krikun98/Skean/pcb/6col/skean.kicad_sch

## KiCad design pcb/6col/skean.kicad_sch (2023-03-14)

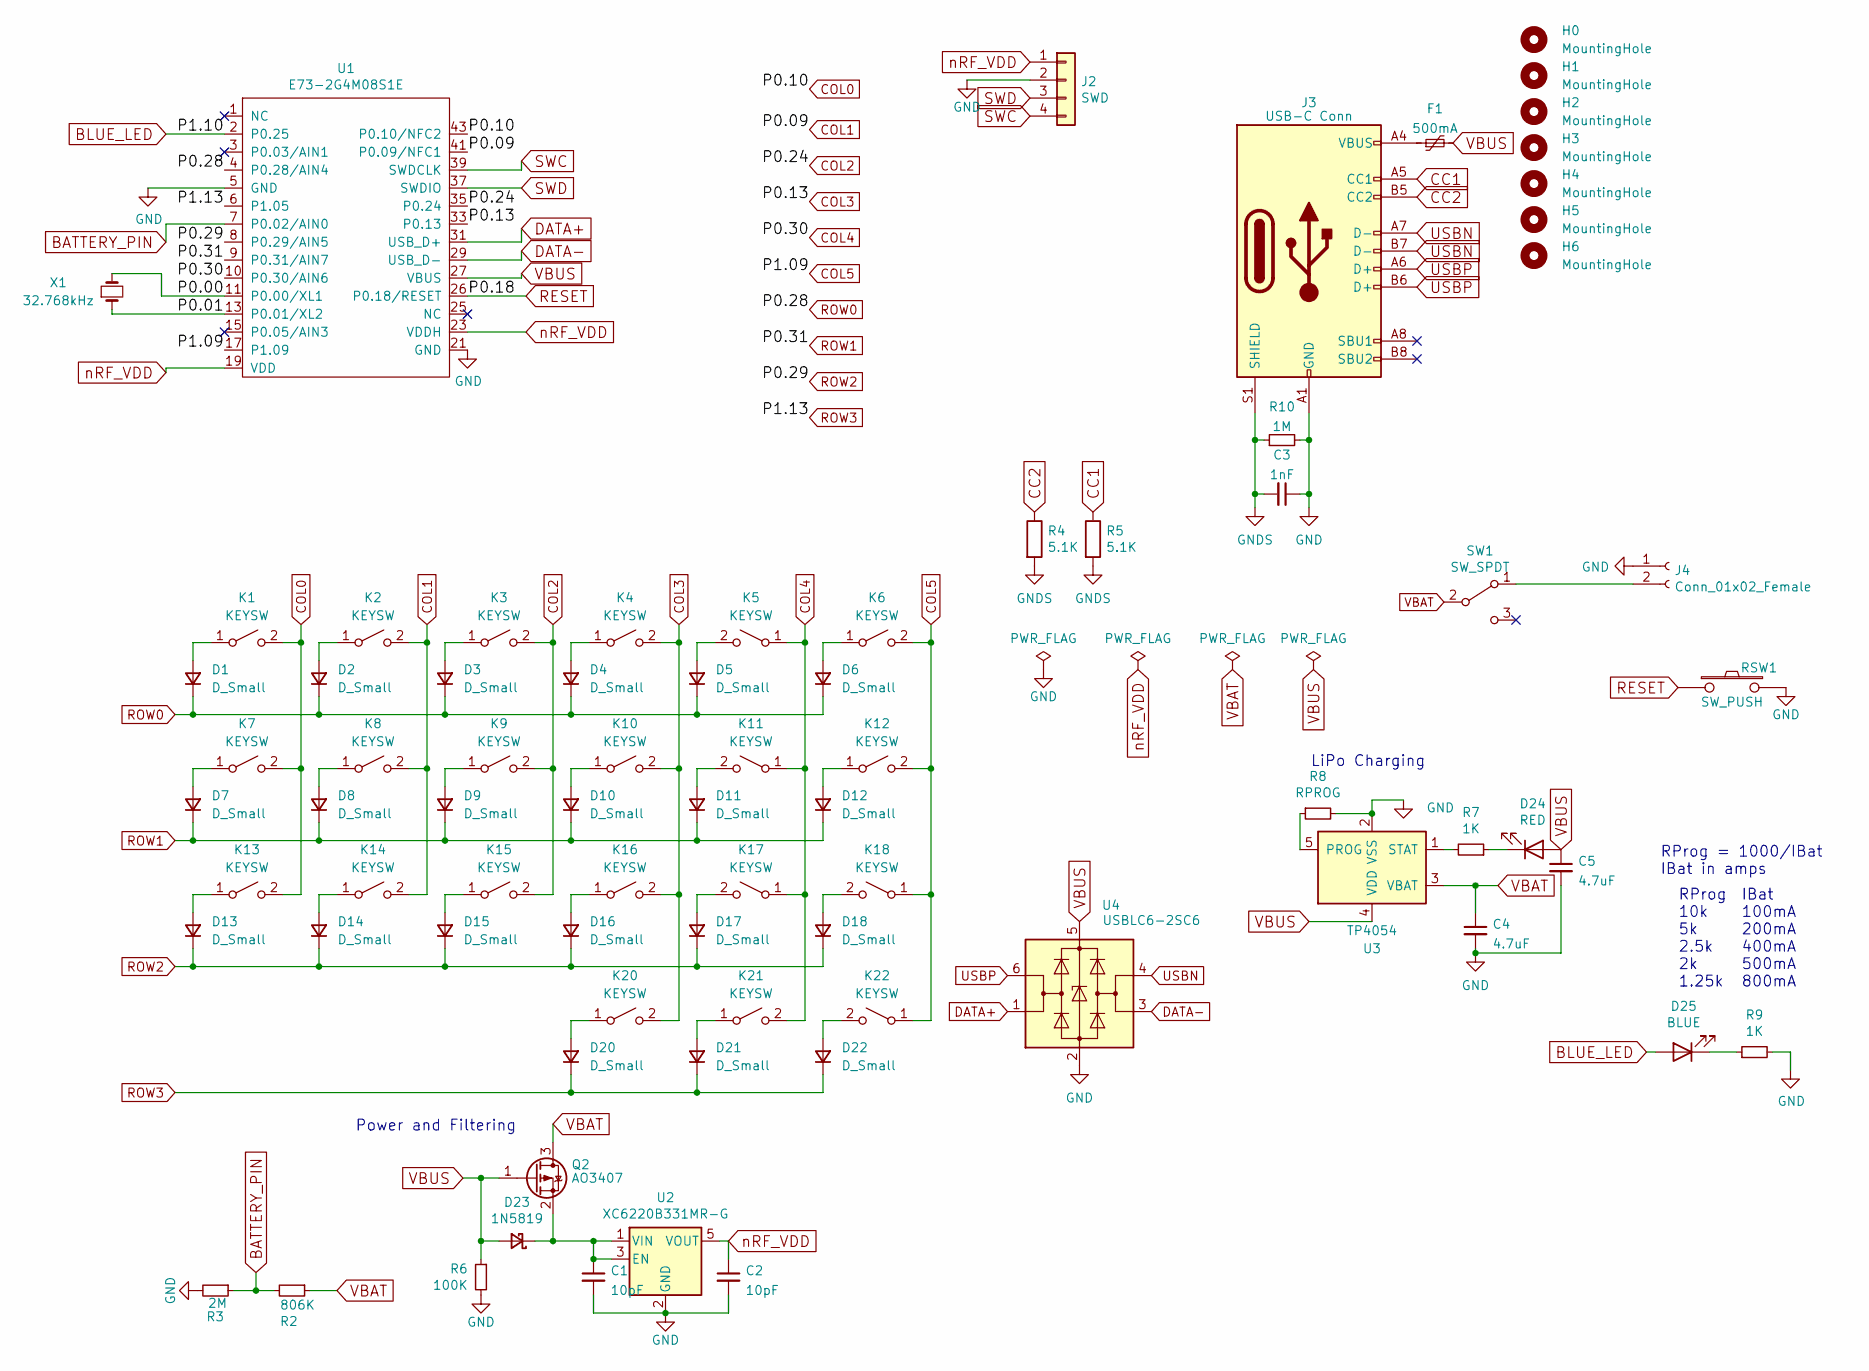
[picture p3: schematic skean.kicad_sch]

Parts:
C1, C2: 10pF; C_0603_1608Metric_REV; LCSC C1634
C3: 1nF; C_0603_1608Metric_REV; LCSC C1588
C4, C5: 4.7uF; C_0603_1608Metric_REV; LCSC C19666
D1, D2, D3, D4, D5, D6, D7, D8, D9, D10, D11, D12, D13, D14, D15, D16, D17, D18, D20, D21, D22: D_Small; D3_SMD
D23: 1N5819; D_SOD-323_HandSoldering_REV
D24: RED; LED_0603_1608Metric_REV
D25: BLUE; LED_0603_1608Metric_REV
F1: 500mA; Fuse_1206_3216Metric_REV; LCSC C883122
H0, H1, H2, H3, H4, H5, H6: MountingHole; M2-MountingHole-Standoff
J2: SWD; connector_swd_REV
J3: USB-C Conn; USB-C_C168688_REV_V2
J4: Conn_01x02_Female; Battery_TH
K1, K2, K3, K4, K5, K6, K7, K8, K9, K10, K11, K12, K13, K14, K15, K16, K17, K20, K21: KEYSW; MX-Alps-Omron-SKCC-Hitek-Futaba-MA-1U-REV
K18: KEYSW; MX-Alps-Omron-SKCC-Inv-Hitek-Futaba-MA-1U-REV
K22: KEYSW; MX-Alps-Omron-SKCC-Hitek-Futaba-MA-1.5U-REV
Q2: AO3407; SOT-23_Handsoldering_REV
R2: 806K; R_0603_1608Metric_REV
R3: 2M; R_0603_1608Metric_REV
R4, R5: 5.1K; R_0603_1608Metric_REV
R6: 100K; R_0603_1608Metric_REV
R7, R9: 1K; R_0603_1608Metric_REV
R8: RPROG; R_0603_1608Metric_REV
R10: 1M; R_0603_1608Metric_REV; LCSC C22935
RSW1: SW_PUSH; SW_SPST_EVQP7C_REV
SW1: SW_SPDT; SW_SPDT+H-MSK12C01_hor(7pin_SMD)_REV
U1: E73-2G4M08S1E; E73-2G4M08S1E-52833_REV
U2: XC6220B331MR-G; SOT-23-5_HandSoldering_REV
U3: TP4054; SOT-23-5_HandSoldering_REV
U4: USBLC6-2SC6; SOT-23-6_Handsoldering_REV; LCSC C558442
X1: 32.768kHz; Crystal_SMD_MicroCrystal_CM9V-T1A-2Pin_1.6x1.0mm_HandSolder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

Connections:
BATTERY_PIN: R2.2, R3.1, U1.7 (P0.02/AIN0)
BLUE_LED: D25.2 (A), U1.2 (P0.25)
CC1: J3.A5 (CC1), R5.1
CC2: J3.B5 (CC2), R4.1
COL0: K1.2 (B), K7.2 (B), K13.2 (B), U1.43 (P0.10/NFC2)
COL1: K2.2 (B), K8.2 (B), K14.2 (B), U1.41 (P0.09/NFC1)
COL2: K3.2 (B), K9.2 (B), K15.2 (B), U1.35 (P0.24)
COL3: K4.2 (B), K10.2 (B), K16.2 (B), K20.2 (B), U1.33 (P0.13)
COL4: K5.1 (A), K11.1 (A), K17.1 (A), K21.2 (B), U1.10 (P0.30/AIN6)
COL5: K6.2 (B), K12.2 (B), K18.1 (A), K22.1 (A), U1.17 (P1.09)
DATA+: U1.31 (USB_D+), U4.1 (I/O1)
DATA-: U1.29 (USB_D-), U4.3 (I/O2)
GND: C1.2, C2.2, C3.1, C4.2, C5.2, J2.2, J3.A1 (GND), J3.A12 (GND), J3.B1 (GND), J3.B12 (GND), J4.1, R3.2, R6.2, R8.2, R9.2, R10.2, RSW1.2, U1.5 (GND), U1.21 (GND), U2.2 (GND), U3.2 (VSS), U4.2 (GND)
GNDS: C3.2, J3.S1 (SHIELD), R4.2, R5.2, R10.1
unnamed: C1.1, D23.1 (K), Q2.2 (S), U2.1 (VIN), U2.3 (EN)
unnamed: D1.2 (A), K1.1 (A)
unnamed: D2.2 (A), K2.1 (A)
unnamed: D3.2 (A), K3.1 (A)
unnamed: D4.2 (A), K4.1 (A)
unnamed: D5.2 (A), K5.2 (B)
unnamed: D6.2 (A), K6.1 (A)
unnamed: D7.2 (A), K7.1 (A)
unnamed: D8.2 (A), K8.1 (A)
unnamed: D9.2 (A), K9.1 (A)
unnamed: D10.2 (A), K10.1 (A)
unnamed: D11.2 (A), K11.2 (B)
unnamed: D12.2 (A), K12.1 (A)
unnamed: D13.2 (A), K13.1 (A)
unnamed: D14.2 (A), K14.1 (A)
unnamed: D15.2 (A), K15.1 (A)
unnamed: D16.2 (A), K16.1 (A)
unnamed: D17.2 (A), K17.2 (B)
unnamed: D18.2 (A), K18.2 (B)
unnamed: D20.2 (A), K20.1 (A)
unnamed: D21.2 (A), K21.1 (A)
unnamed: D22.2 (A), K22.2 (B)
unnamed: D24.1 (K), R7.1
unnamed: D25.1 (K), R9.1
unnamed: F1.1, J3.A4 (VBUS), J3.A9 (VBUS), J3.B4 (VBUS), J3.B9 (VBUS)
unnamed: J4.2, SW1.1 (A)
unnamed: R7.2, U3.1 (STAT)
unnamed: R8.1, U3.5 (PROG)
P0.00: U1.11 (P0.00/XL1), X1.2
P0.01: U1.13 (P0.01/XL2), X1.1
RESET: RSW1.1, U1.26 (P0.18/RESET)
ROW0: D1.1 (K), D2.1 (K), D3.1 (K), D4.1 (K), D5.1 (K), D6.1 (K), U1.4 (P0.28/AIN4)
ROW1: D7.1 (K), D8.1 (K), D9.1 (K), D10.1 (K), D11.1 (K), D12.1 (K), U1.9 (P0.31/AIN7)
ROW2: D13.1 (K), D14.1 (K), D15.1 (K), D16.1 (K), D17.1 (K), D18.1 (K), U1.8 (P0.29/AIN5)
ROW3: D20.1 (K), D21.1 (K), D22.1 (K), U1.6 (P1.05)
SWC: J2.4, U1.39 (SWDCLK)
SWD: J2.3, U1.37 (SWDIO)
USBN: J3.A7 (D-), J3.B7 (D-), U4.4 (I/O2)
USBP: J3.A6 (D+), J3.B6 (D+), U4.6 (I/O1)
VBAT: C4.1, Q2.3 (D), R2.1, SW1.2 (B), U3.3 (VBAT)
VBUS: C5.1, D23.2 (A), D24.2 (A), F1.2, Q2.1 (G), R6.1, U1.27 (VBUS), U3.4 (VDD), U4.5 (VBUS)
nRF_VDD: C2.1, J2.1, U1.19 (VDD), U1.23 (VDDH), U2.5 (VOUT)

Notes on the sheet:
LiPo Charging
RProg = 1000/IBat IBat in amps
IBat 100mA 200mA 400mA 500mA 800mA
Power and Filtering
RProg 10k 5k 2.5k 2k 1.25k
